Ralidaer/PhotovoltaicSystem/Photos/IMG_20210707_111322.jpg

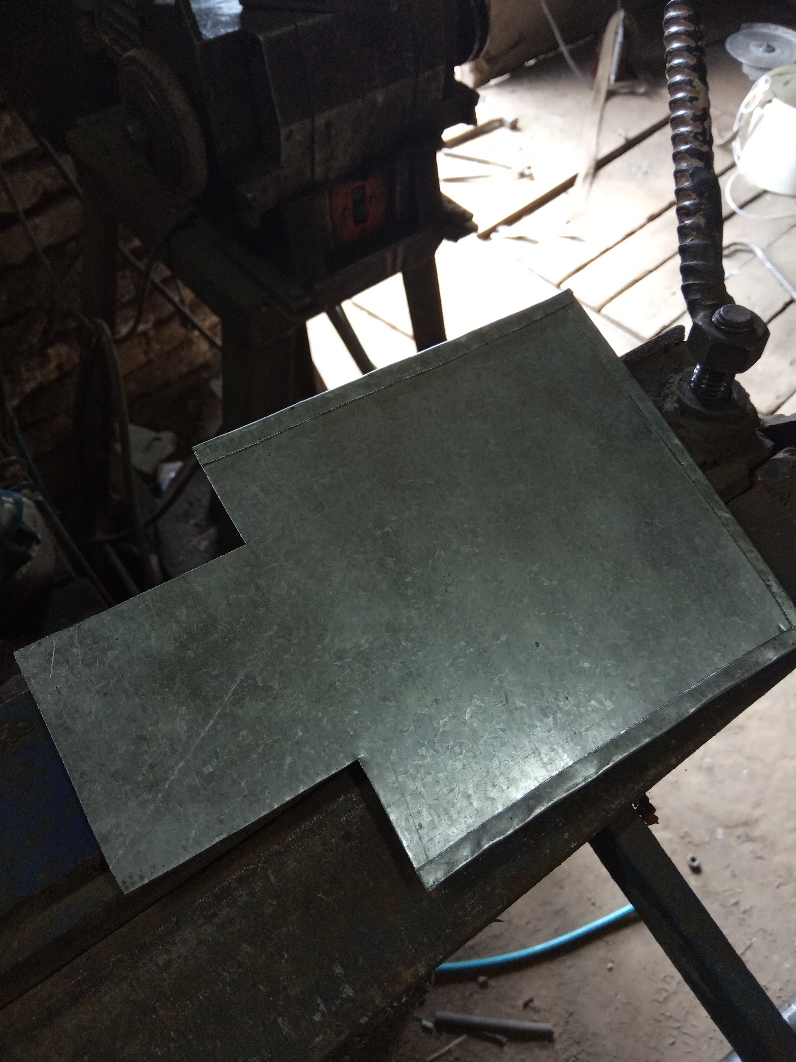
Photos/IMG_20210707_111322.jpg
