Ralidaer/PhotovoltaicSystem/Photos/IMG_20210707_111331.jpg

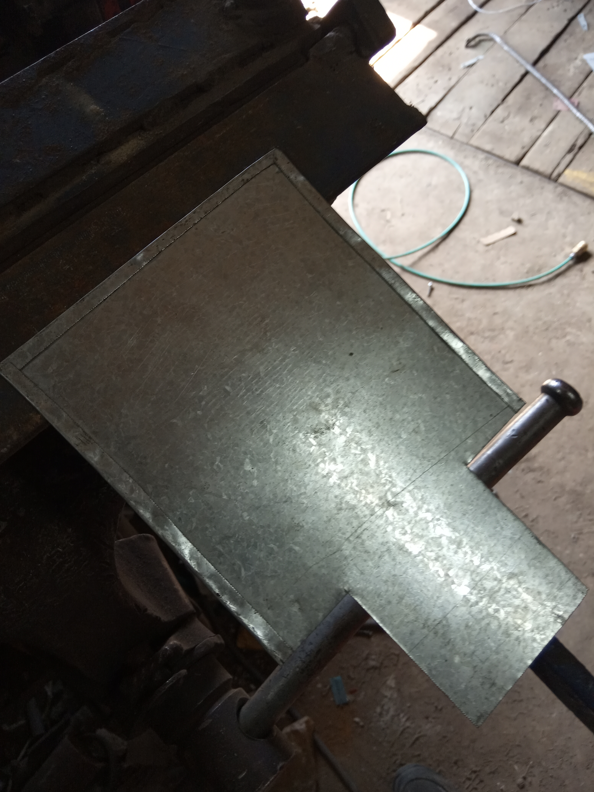
Photos/IMG_20210707_111331.jpg
