Ralidaer/PhotovoltaicSystem/Photos/IMG_20210707_111337.jpg

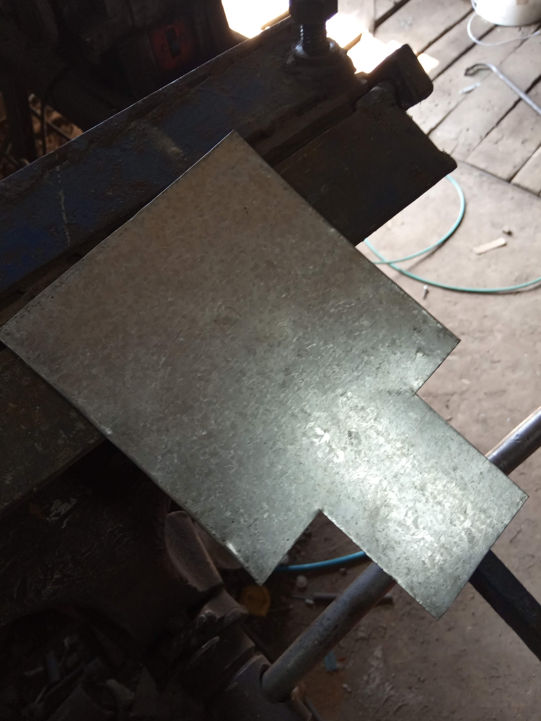
Photos/IMG_20210707_111337.jpg
