Ralidaer/PhotovoltaicSystem/Photos/IMG_20210707_163816.jpg

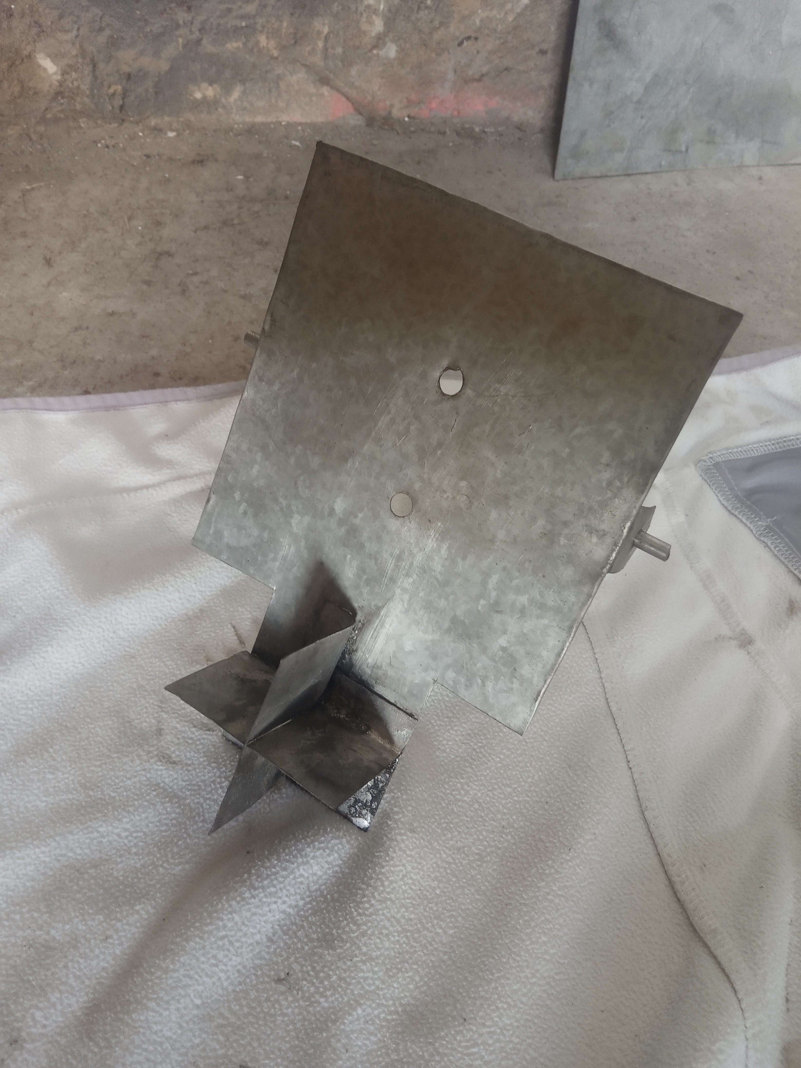
Photos/IMG_20210707_163816.jpg
