Ralidaer/PhotovoltaicSystem/Photos/IMG_20210707_163824.jpg

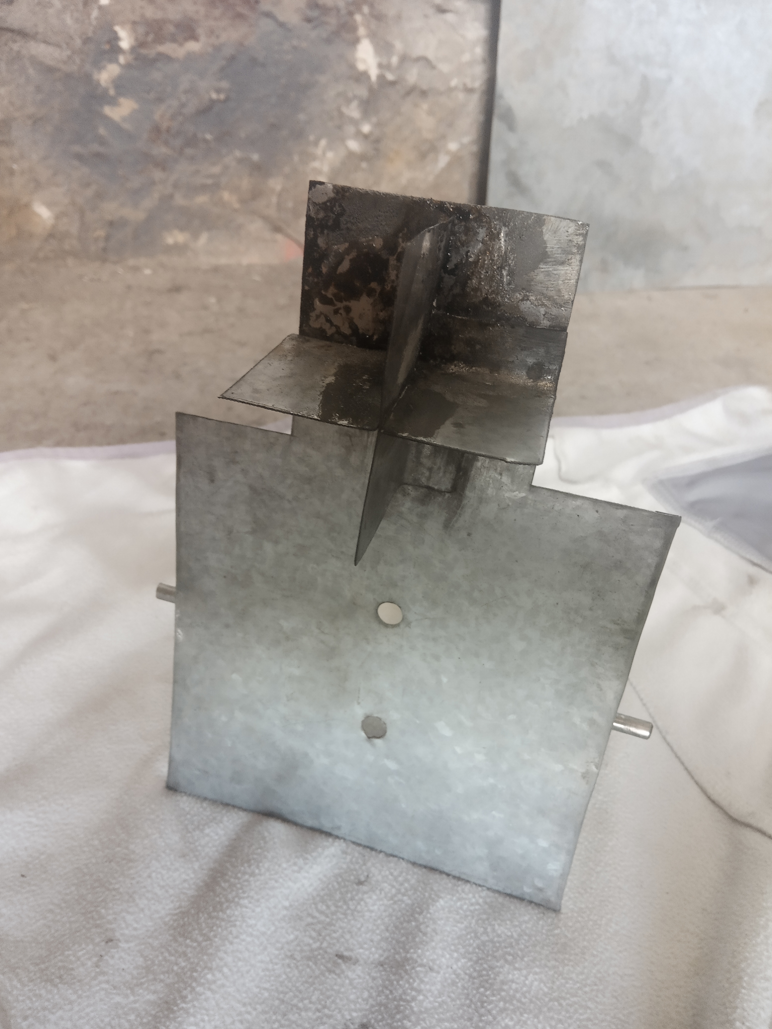
Photos/IMG_20210707_163824.jpg
