Ralidaer/PhotovoltaicSystem/Photos/IMG_20210707_163836.jpg

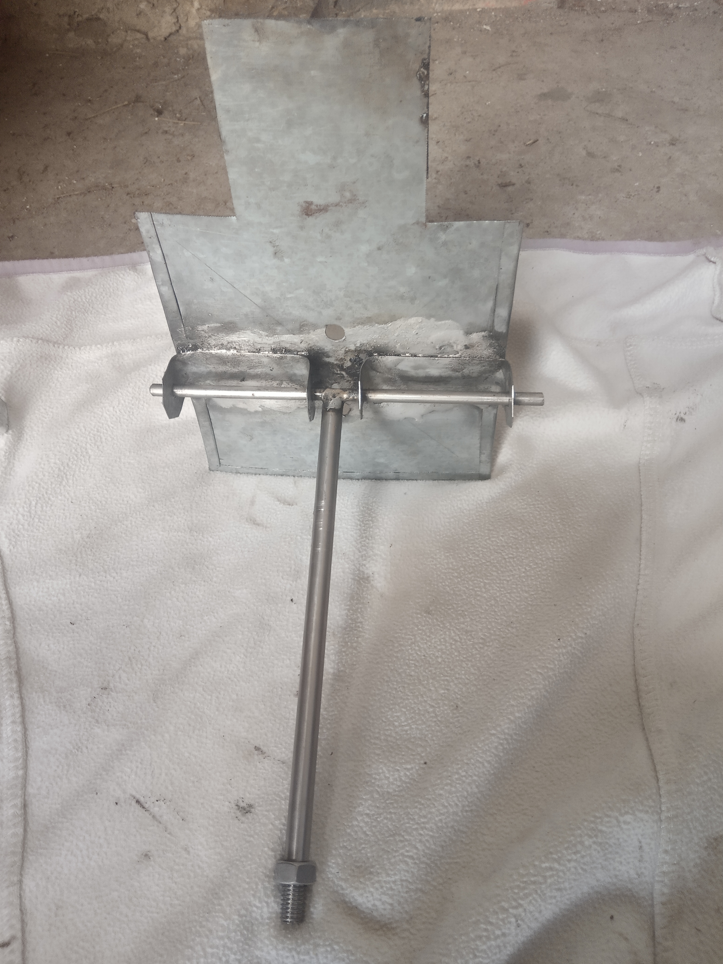
Photos/IMG_20210707_163836.jpg
