Ralidaer/PhotovoltaicSystem/Photos/IMG_20210708_154845.jpg

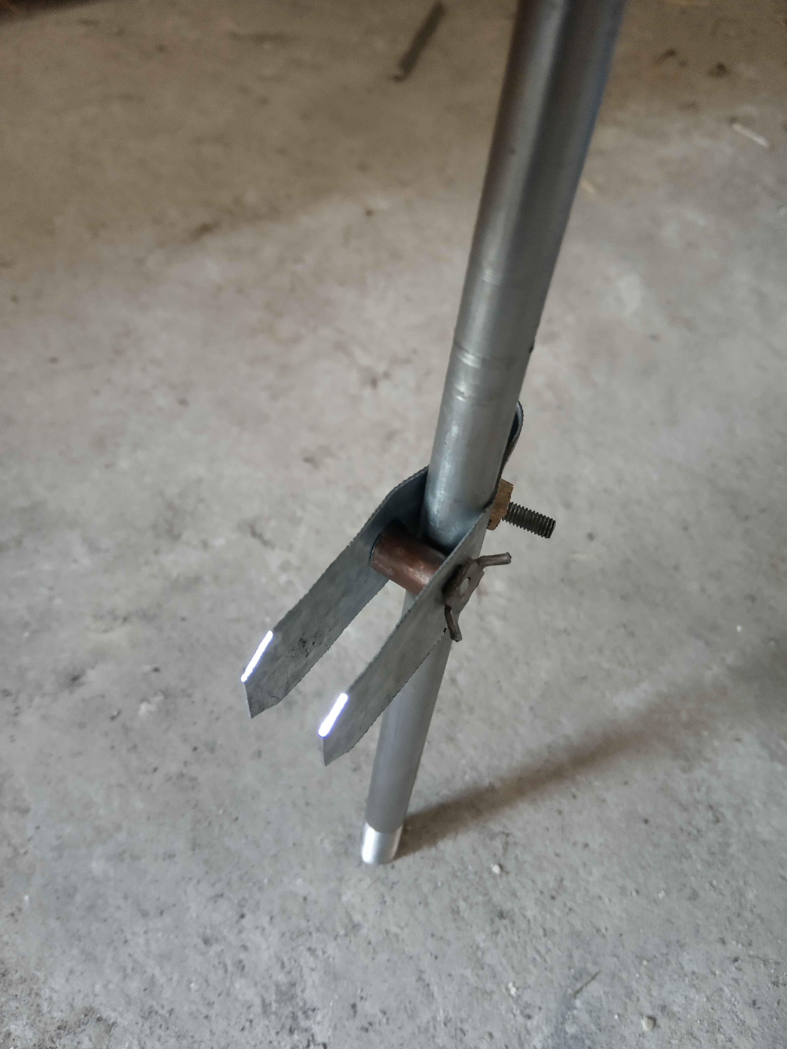
Photos/IMG_20210708_154845.jpg
