Ralidaer/PhotovoltaicSystem/Photos/IMG_20210708_154850.jpg

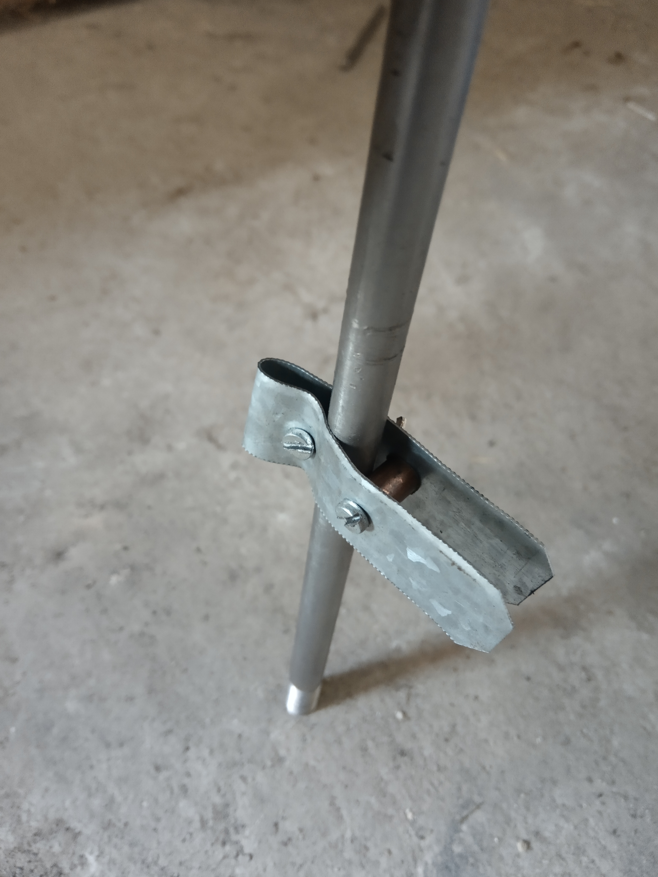
Photos/IMG_20210708_154850.jpg
