Ralidaer/PhotovoltaicSystem/Photos/IMG_20210709_112318.jpg

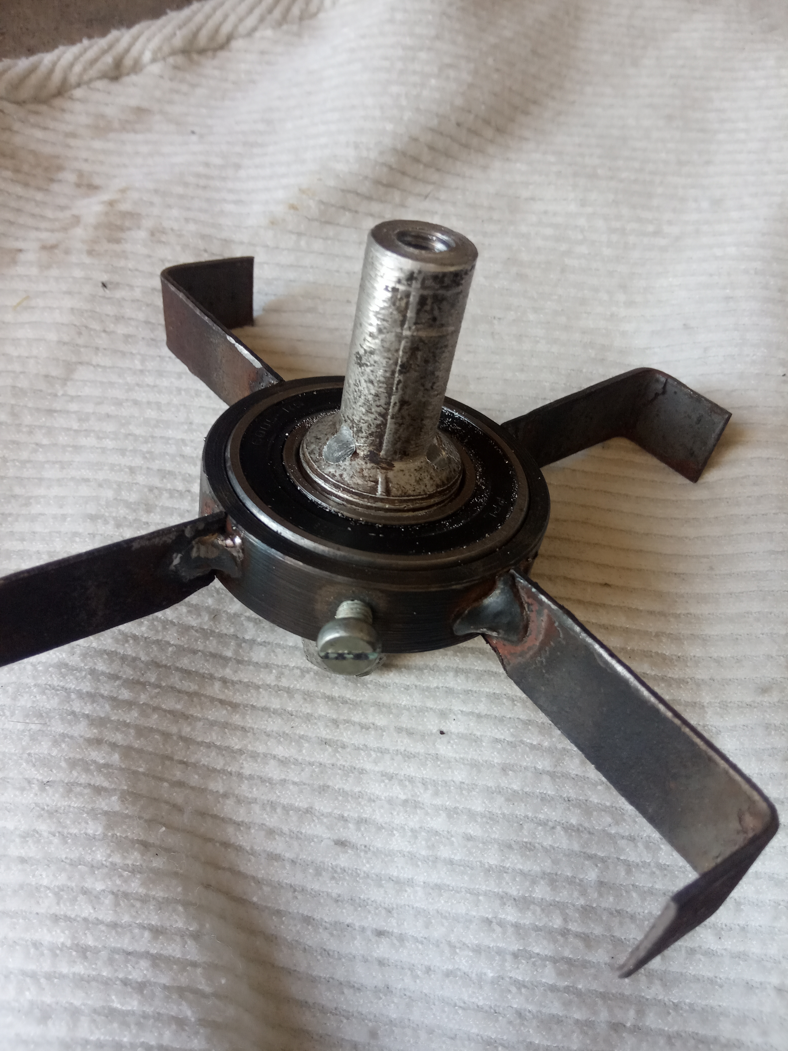
Photos/IMG_20210709_112318.jpg
