Ralidaer/PhotovoltaicSystem/Photos/IMG_20210709_112324.jpg

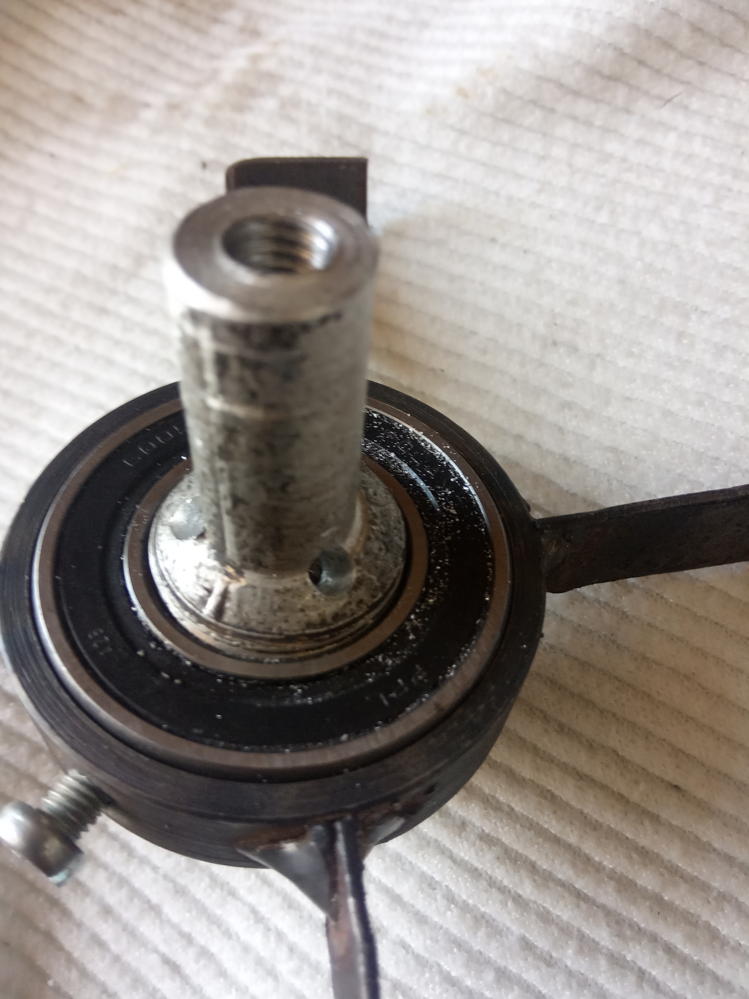
Photos/IMG_20210709_112324.jpg
