Ralidaer/PhotovoltaicSystem/Photos/IMG_20210709_112329.jpg

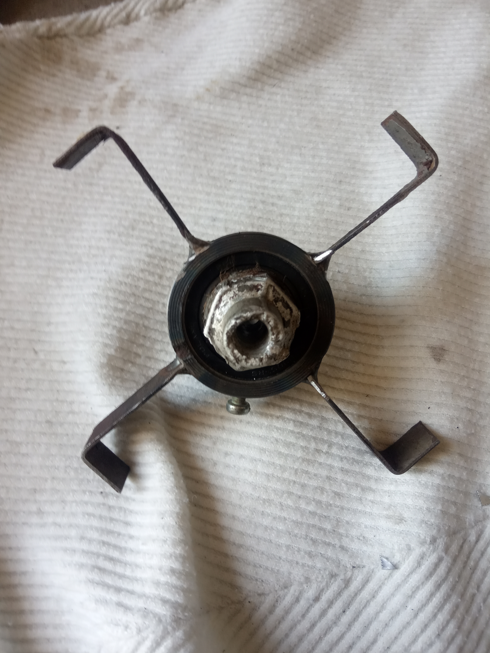
Photos/IMG_20210709_112329.jpg
