Ralidaer/PhotovoltaicSystem/Photos/IMG_20210709_112338.jpg

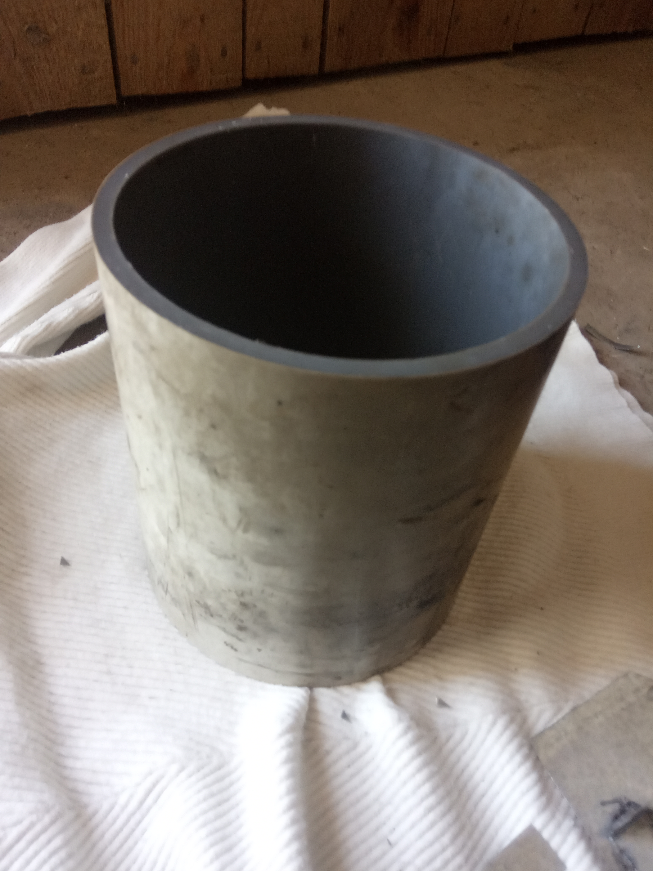
Photos/IMG_20210709_112338.jpg
