Ralidaer/PhotovoltaicSystem/Photos/IMG_20210709_112344.jpg

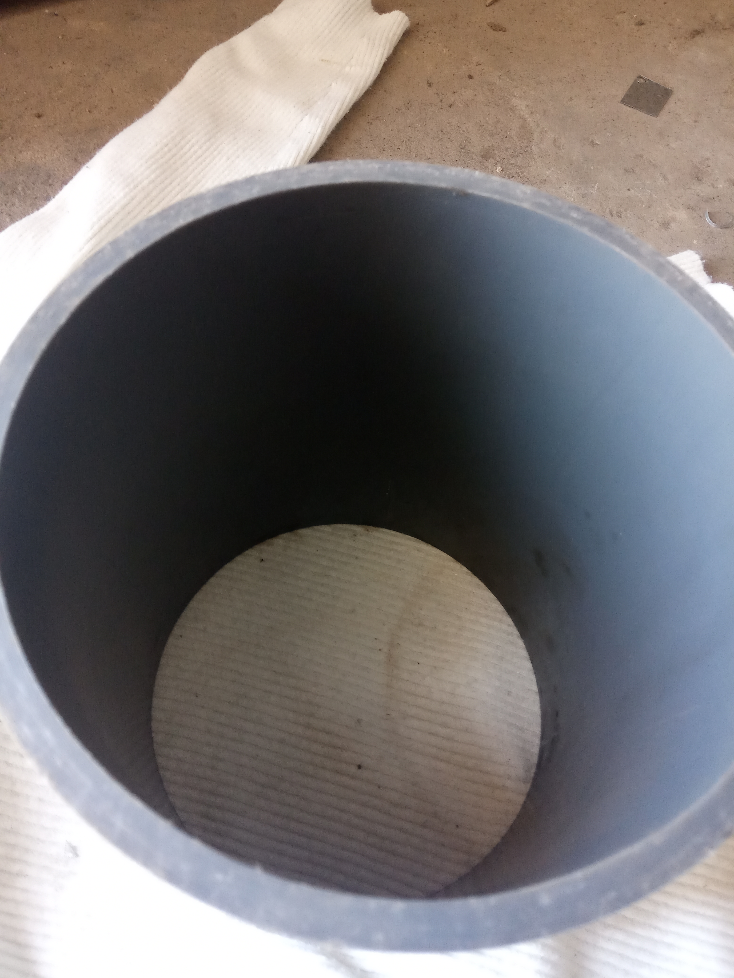
Photos/IMG_20210709_112344.jpg
