Ralidaer/PhotovoltaicSystem/Photos/IMG_20210709_112456.jpg

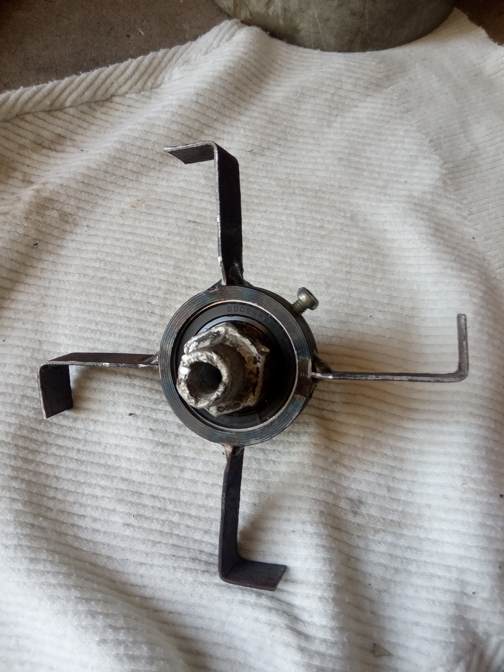
Photos/IMG_20210709_112456.jpg
