Ralidaer/PhotovoltaicSystem/Photos/IMG_20210709_112603.jpg

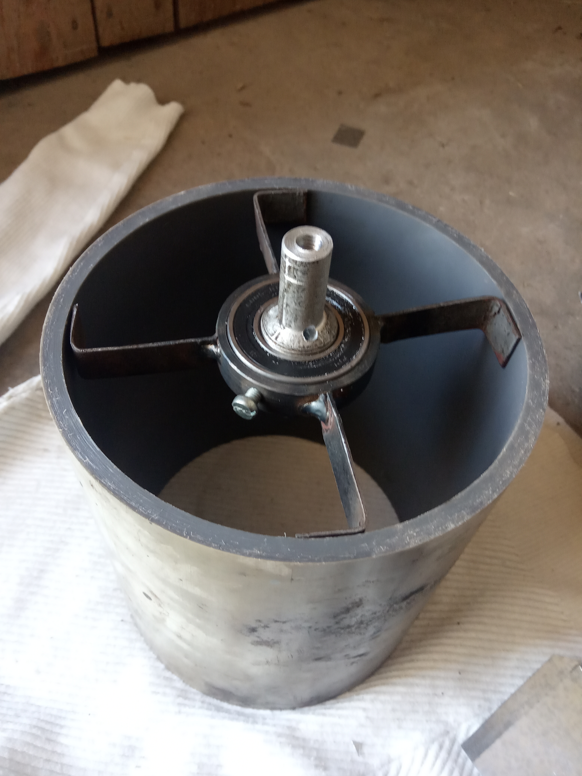
Photos/IMG_20210709_112603.jpg
