Ralidaer/PhotovoltaicSystem/Photos/IMG_20210709_112611.jpg

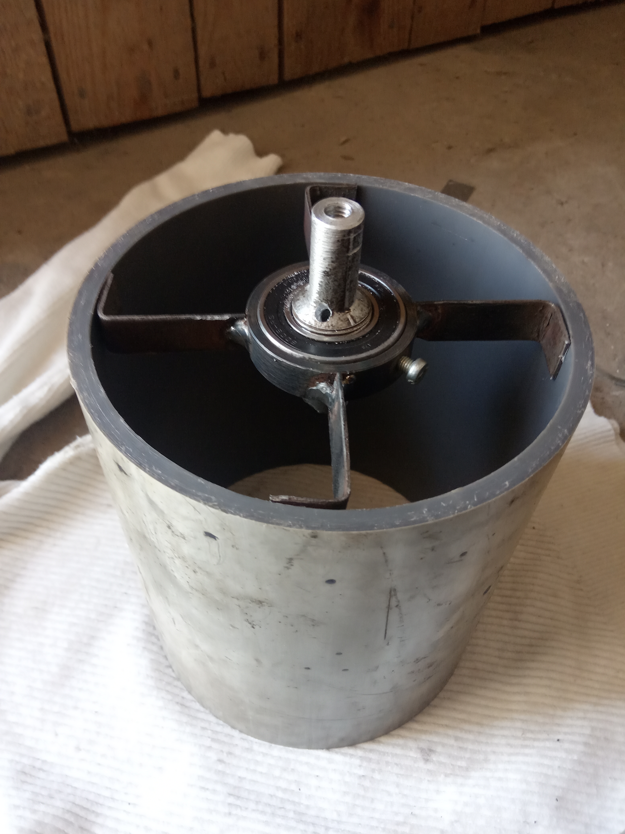
Photos/IMG_20210709_112611.jpg
