Ralidaer/PhotovoltaicSystem/Photos/IMG_20210709_112644.jpg

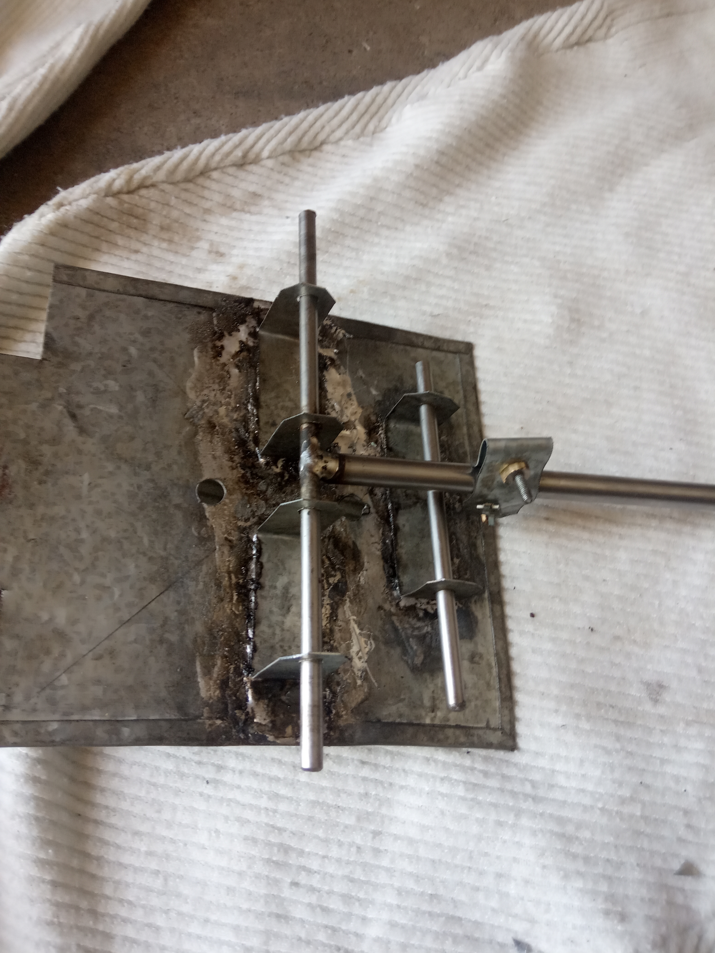
Photos/IMG_20210709_112644.jpg
