Ralidaer/PhotovoltaicSystem/Photos/IMG_20210709_112650.jpg

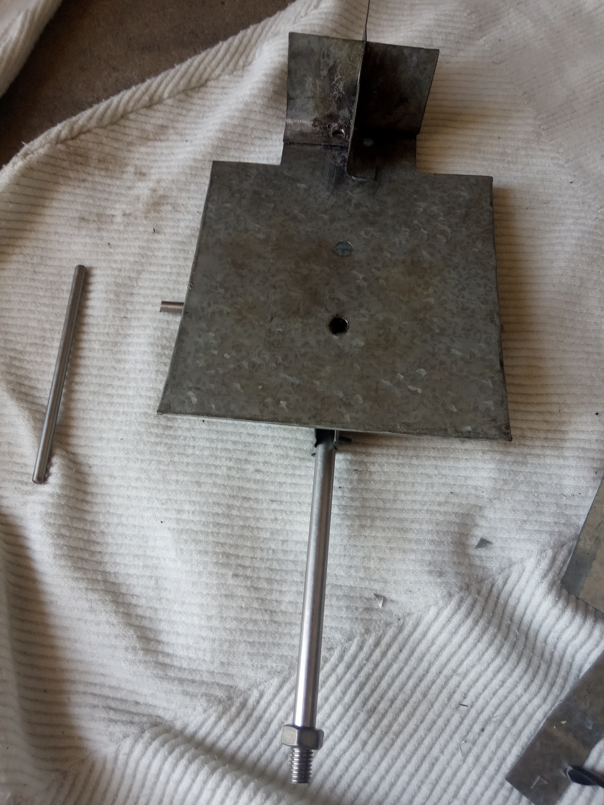
Photos/IMG_20210709_112650.jpg
