Ralidaer/PhotovoltaicSystem/Photos/IMG_20210709_112700.jpg

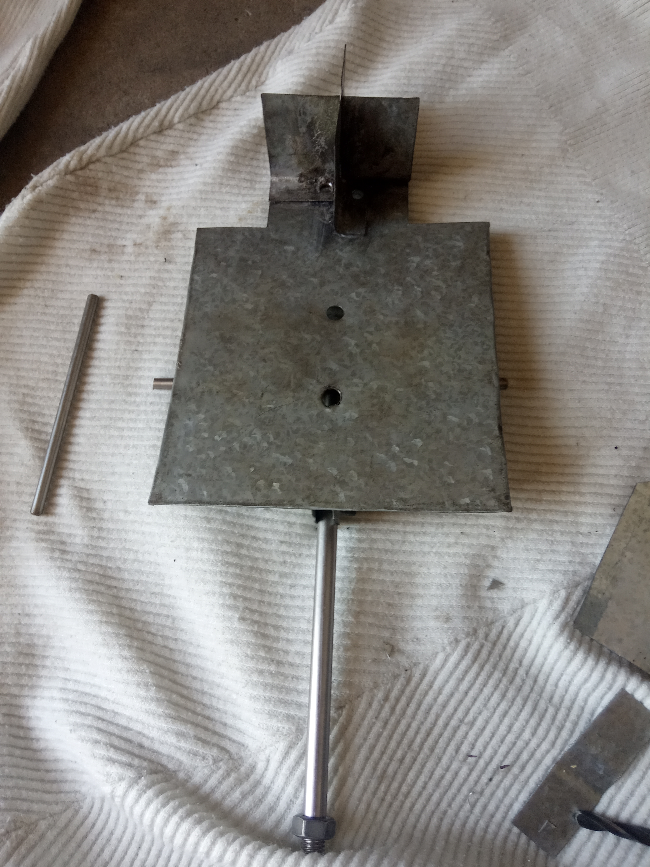
Photos/IMG_20210709_112700.jpg
