Ralidaer/PhotovoltaicSystem/Photos/IMG_20210709_112758.jpg

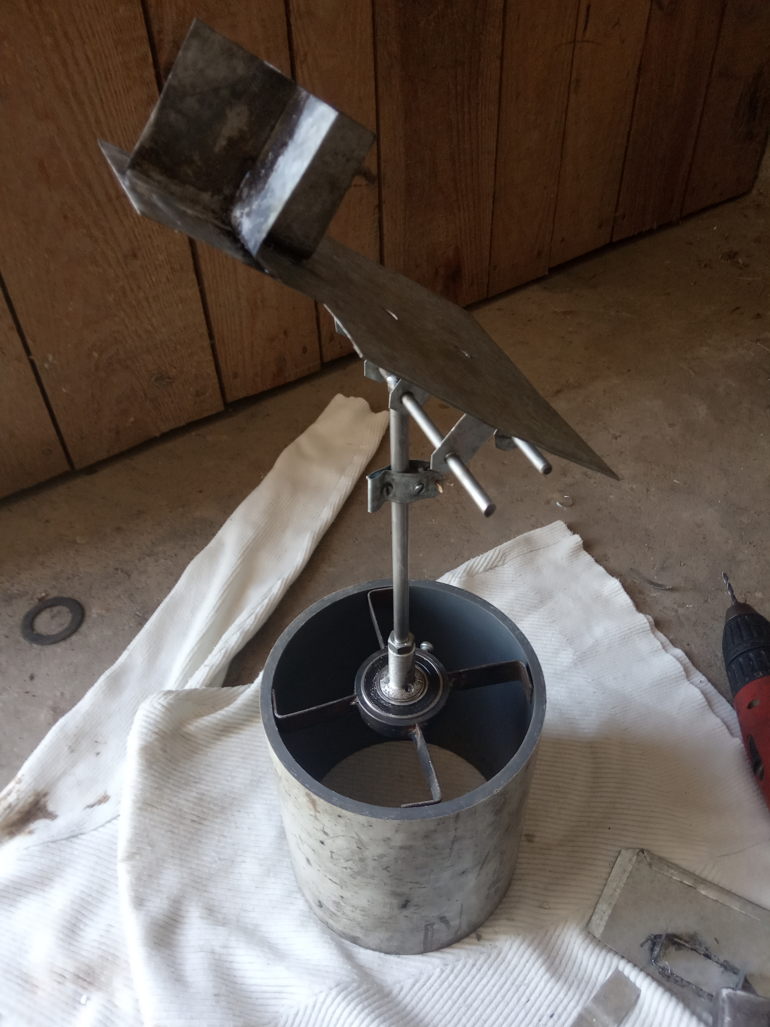
Photos/IMG_20210709_112758.jpg
