Ralidaer/PhotovoltaicSystem/Photos/IMG_20210709_112804.jpg

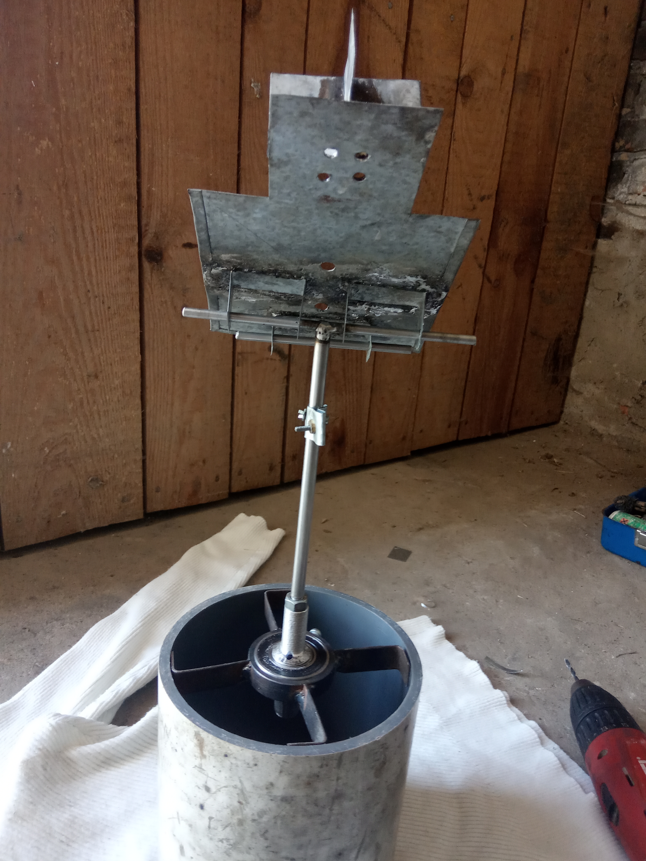
Photos/IMG_20210709_112804.jpg
