Ralidaer/PhotovoltaicSystem/Photos/IMG_20210709_112812.jpg

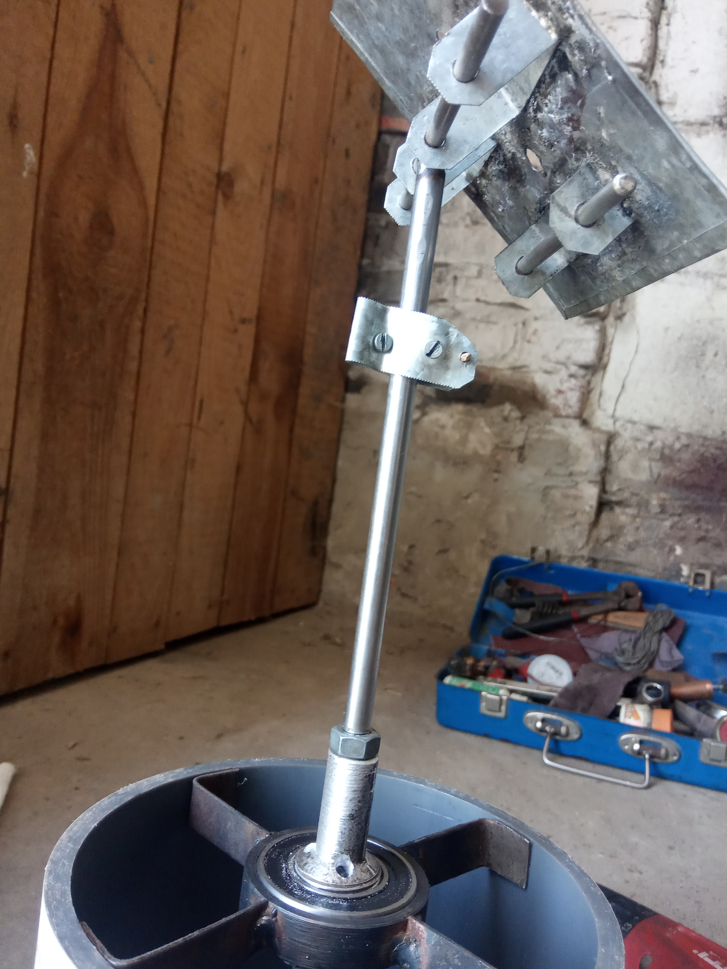
Photos/IMG_20210709_112812.jpg
