Ralidaer/PhotovoltaicSystem/Photos/IMG_20210728_113514.jpg

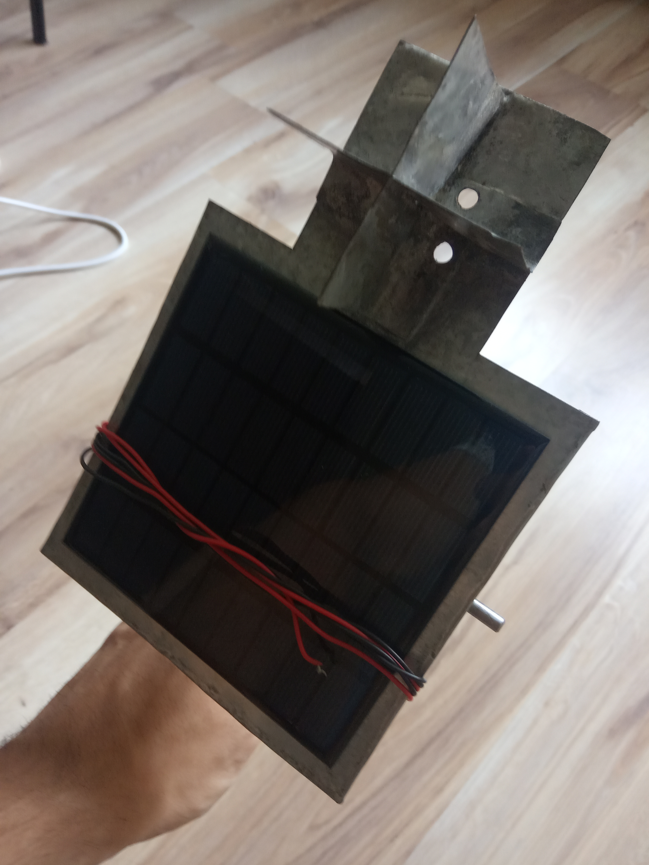
Photos/IMG_20210728_113514.jpg
