Ralidaer/PhotovoltaicSystem/Photos/IMG_20210728_113616.jpg

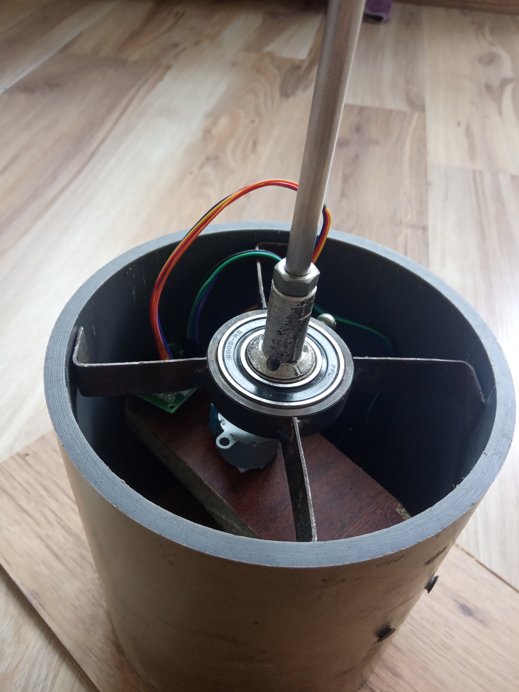
Photos/IMG_20210728_113616.jpg
