Ralidaer/PhotovoltaicSystem/Photos/IMG_20210728_113623.jpg

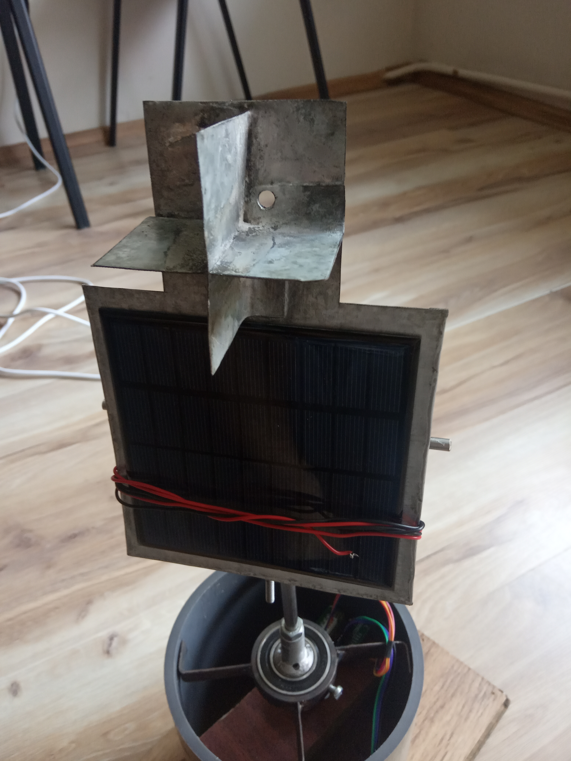
Photos/IMG_20210728_113623.jpg
