Ralidaer/PhotovoltaicSystem/Photos/IMG_20210728_113631.jpg

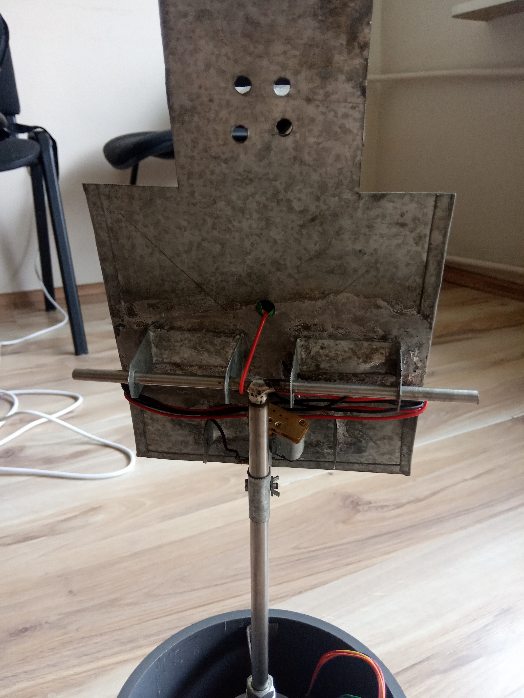
Photos/IMG_20210728_113631.jpg
