Ralidaer/PhotovoltaicSystem/Photos/IMG_20210728_113649.jpg

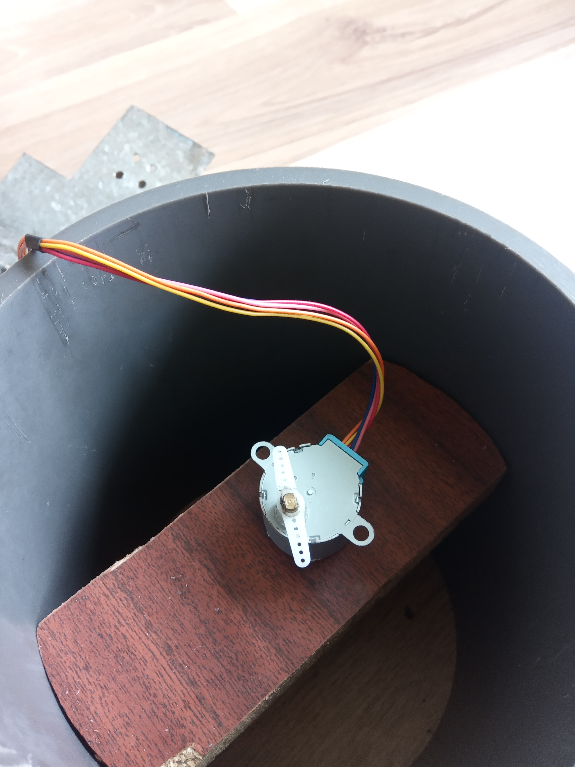
Photos/IMG_20210728_113649.jpg
