Ralidaer/PhotovoltaicSystem/Photos/IMG_20210728_113656.jpg

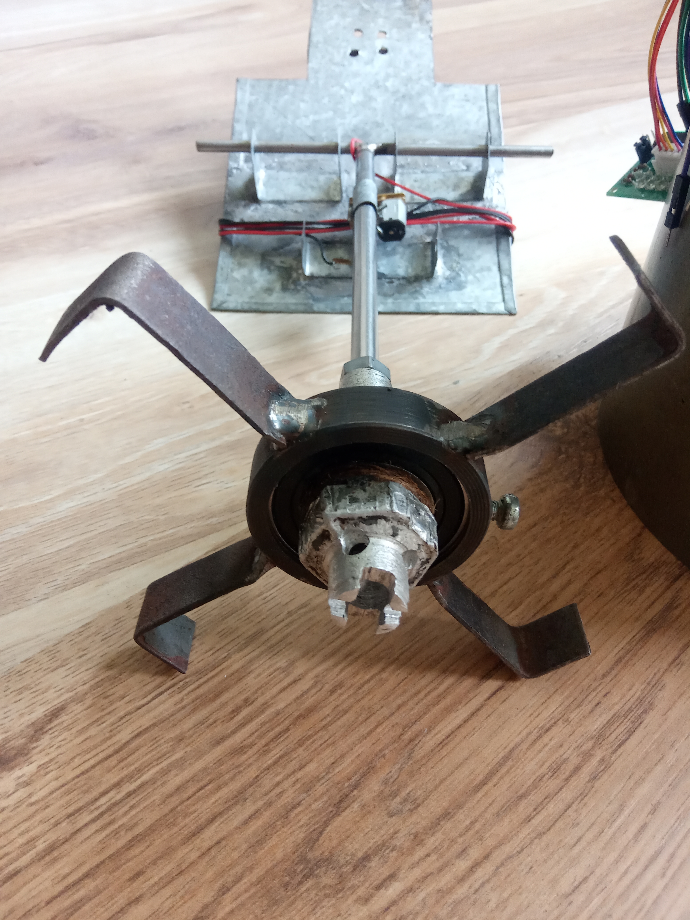
Photos/IMG_20210728_113656.jpg
