Ralidaer/PhotovoltaicSystem/Photos/IMG_20210728_113701.jpg

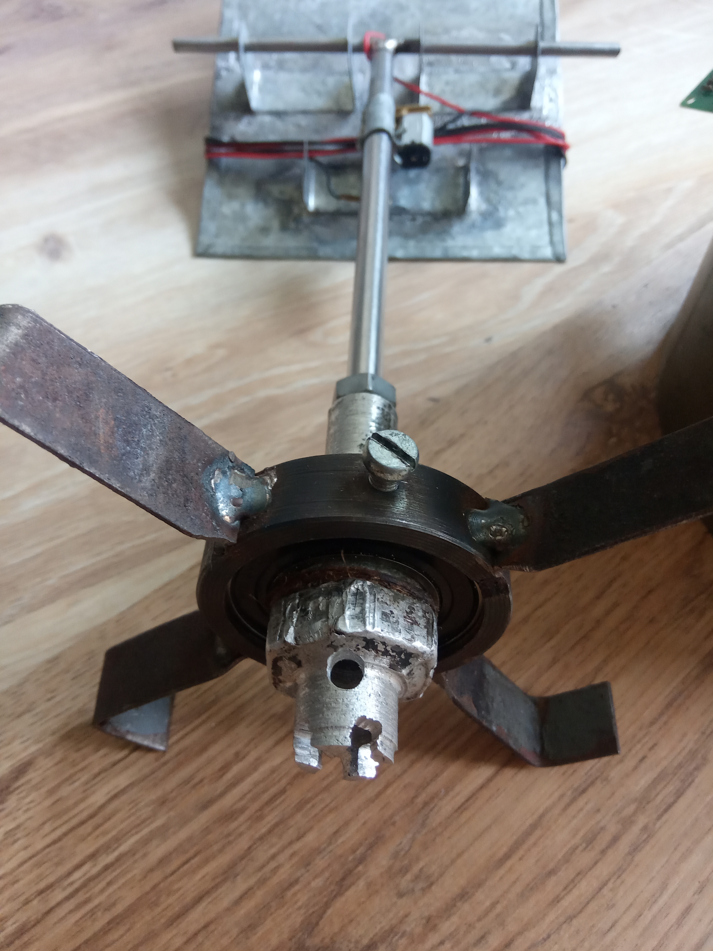
Photos/IMG_20210728_113701.jpg
