Ralidaer/PhotovoltaicSystem/Photos/IMG_20210728_113719.jpg

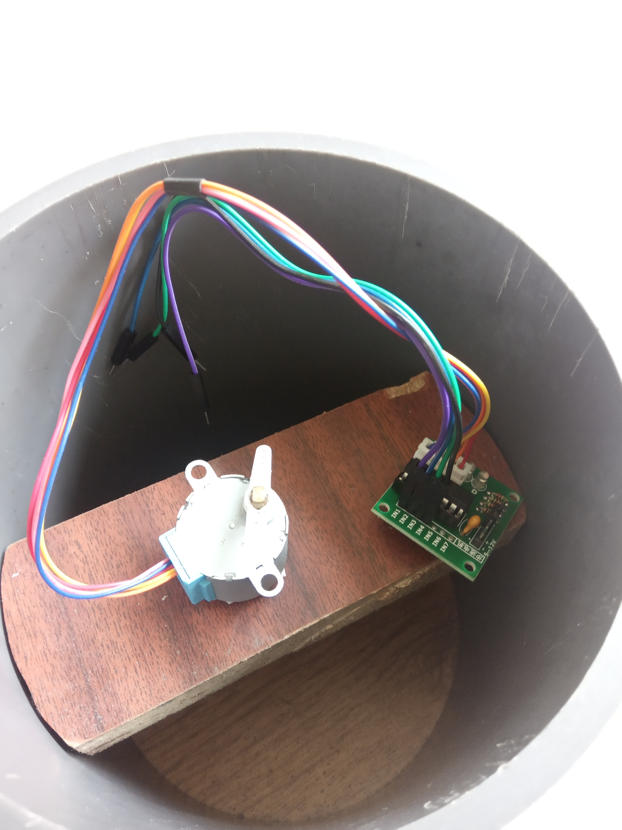
Photos/IMG_20210728_113719.jpg
