Ralidaer/PhotovoltaicSystem/Photos/IMG_20210728_131431.jpg

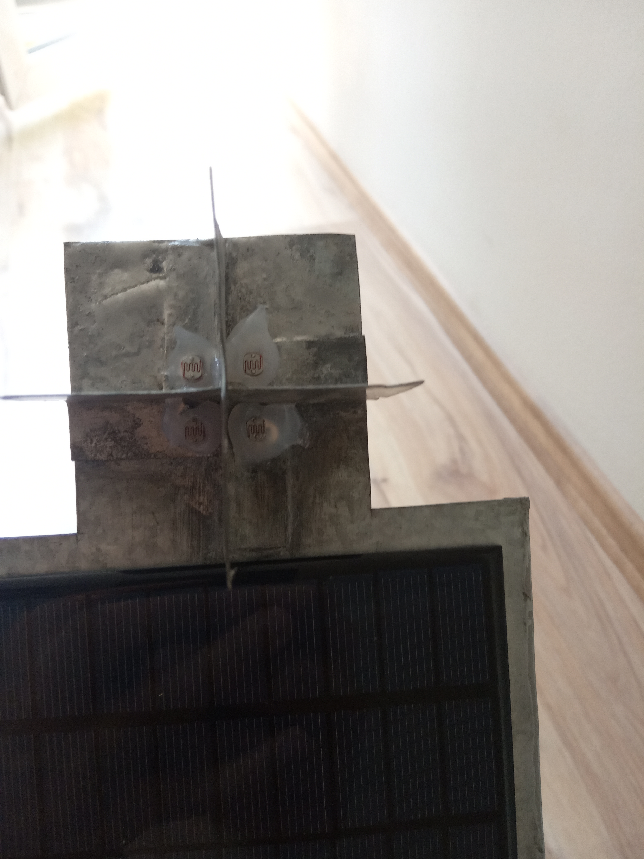
Photos/IMG_20210728_131431.jpg
