Ralidaer/PhotovoltaicSystem/Photos/IMG_20210728_131442.jpg

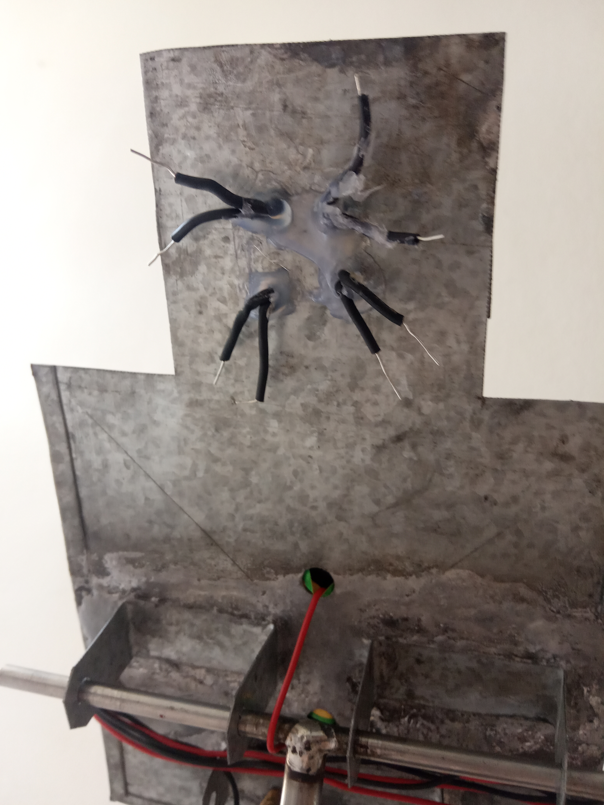
Photos/IMG_20210728_131442.jpg
