Ralidaer/PhotovoltaicSystem/Photos/IMG_20210728_131450.jpg

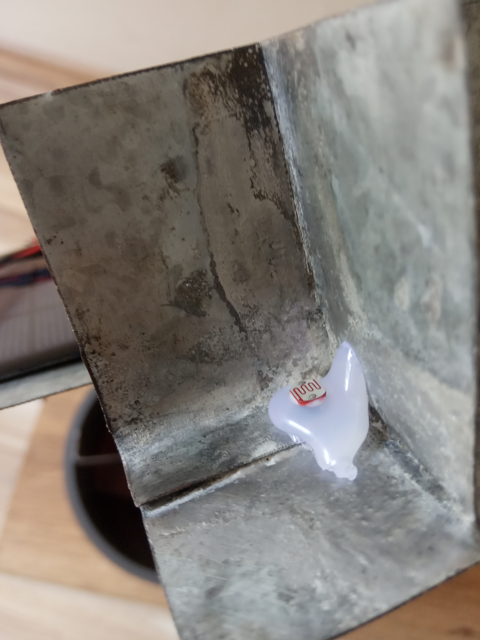
Photos/IMG_20210728_131450.jpg
