Ralidaer/PhotovoltaicSystem/Photos/IMG_20210911_135315.jpg

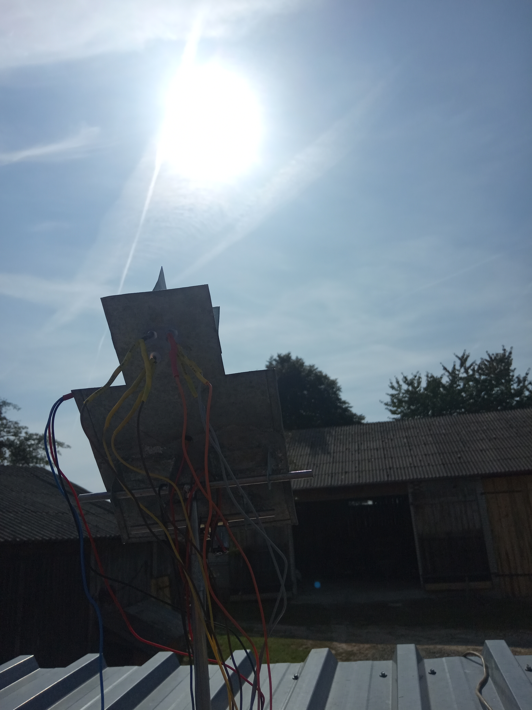
Photos/IMG_20210911_135315.jpg
