Ralidaer/PhotovoltaicSystem/Photos/IMG_20210911_135330.jpg

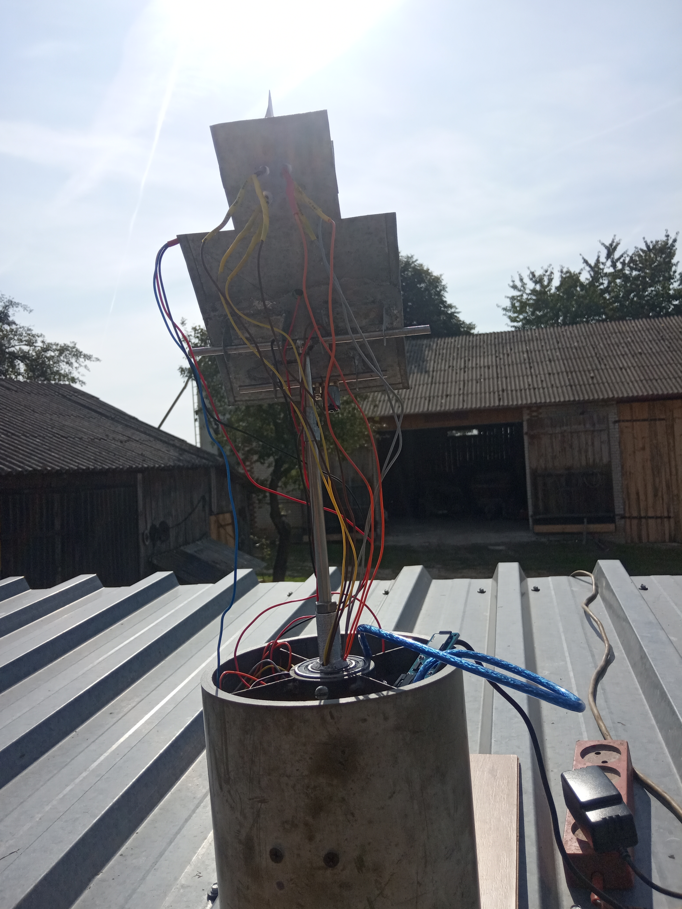
Photos/IMG_20210911_135330.jpg
