Ralidaer/PhotovoltaicSystem/Photos/IMG_20210911_135332.jpg

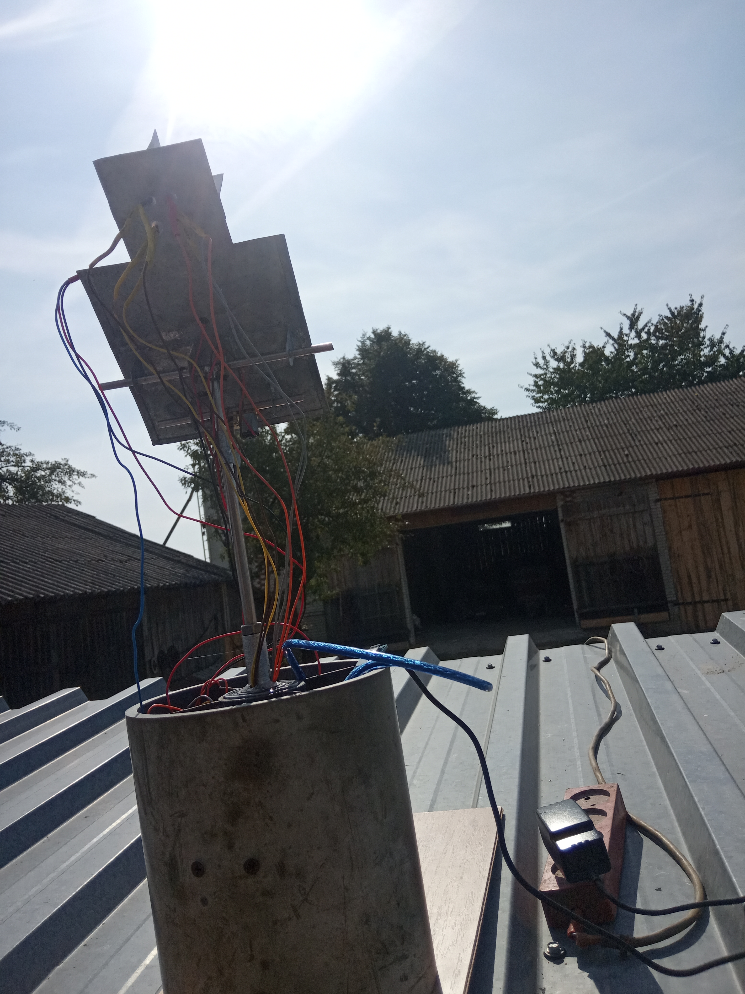
Photos/IMG_20210911_135332.jpg
