Ralidaer/PhotovoltaicSystem/Photos/IMG_20210911_135337.jpg

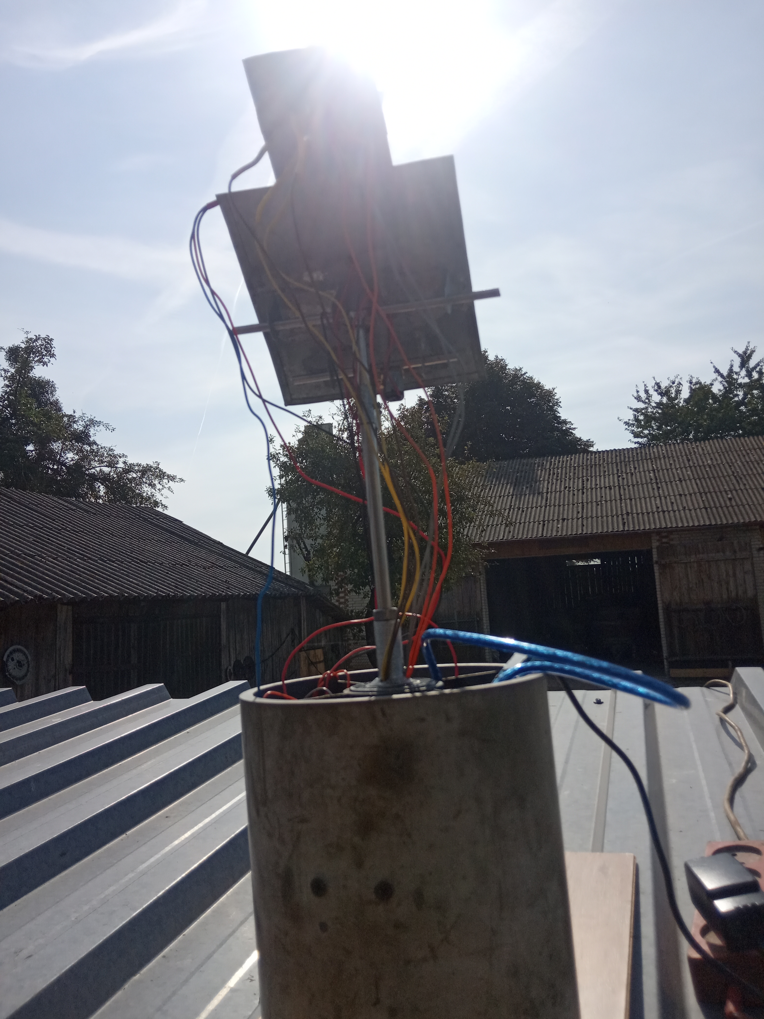
Photos/IMG_20210911_135337.jpg
