Ralidaer/PhotovoltaicSystem/Photos/IMG_20210912_131358.jpg

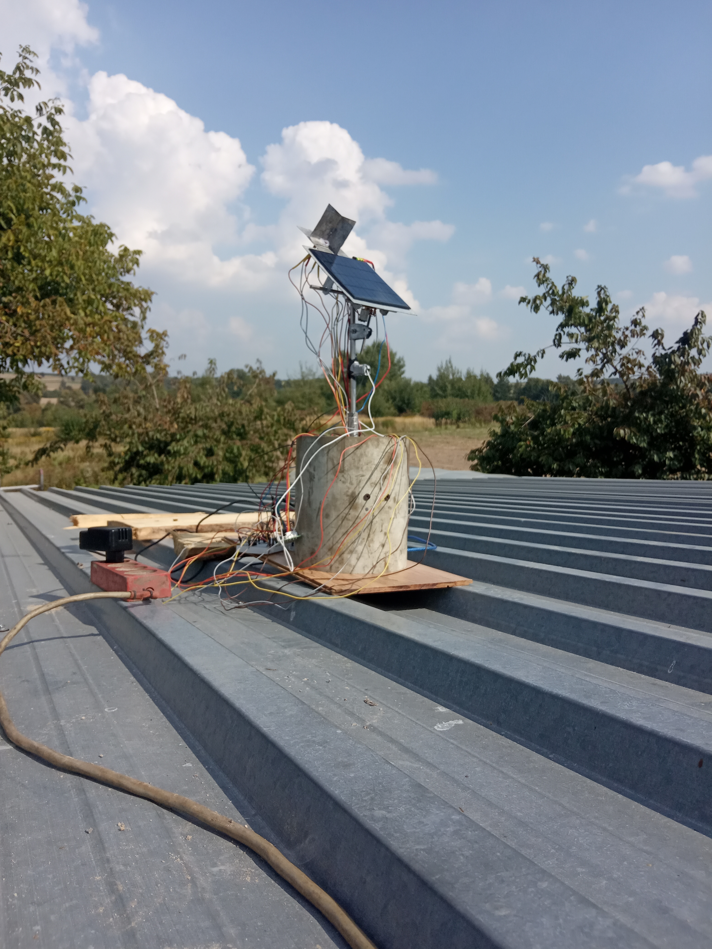
Photos/IMG_20210912_131358.jpg
