Ralidaer/PhotovoltaicSystem/pomiary/analiza/5.38.png

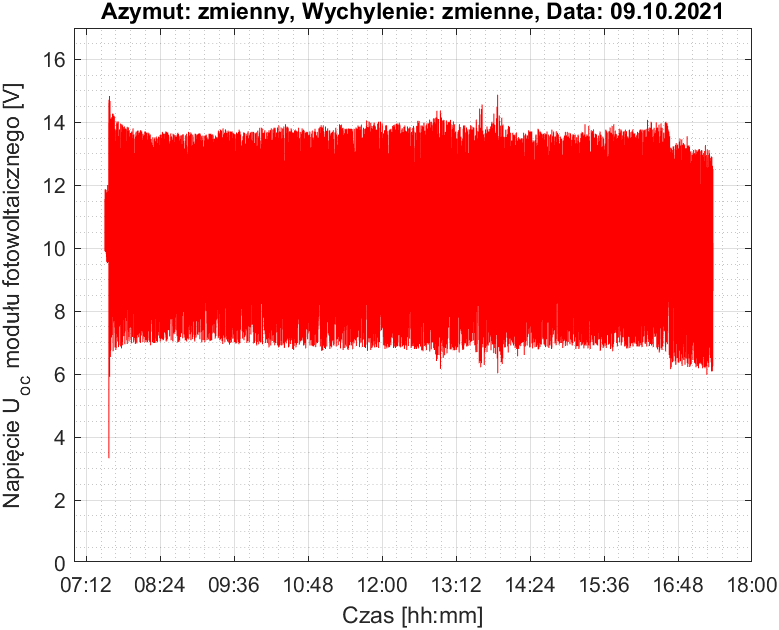
pomiary/analiza/5.38.png
