Ralidaer/PhotovoltaicSystem/pomiary/analiza/5.39.png

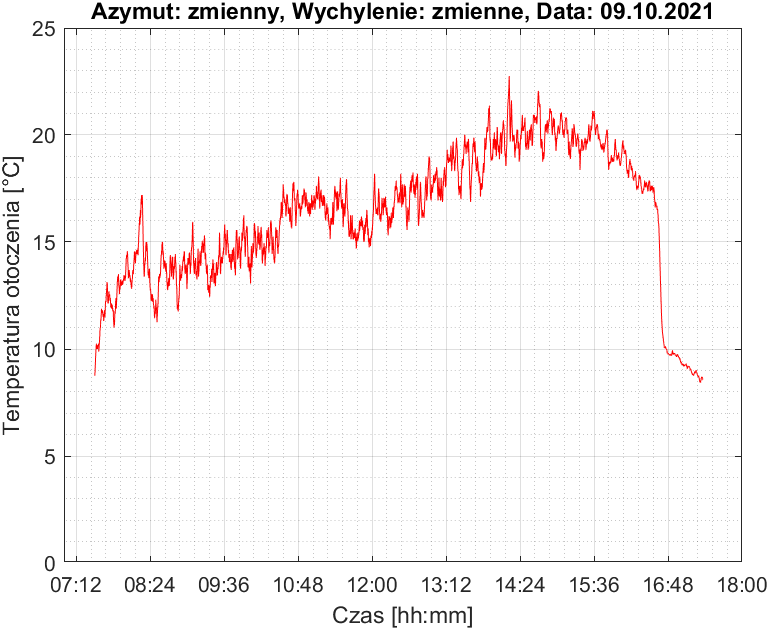
pomiary/analiza/5.39.png
