Ralidaer/PhotovoltaicSystem/pomiary/analiza/5.40.png

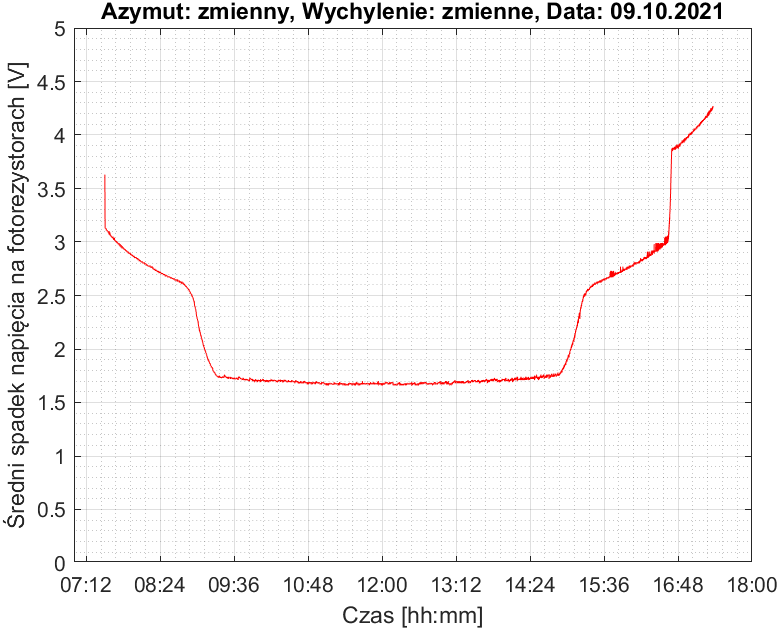
pomiary/analiza/5.40.png
