Ralidaer/PhotovoltaicSystem/pomiary/analiza/5.41.png

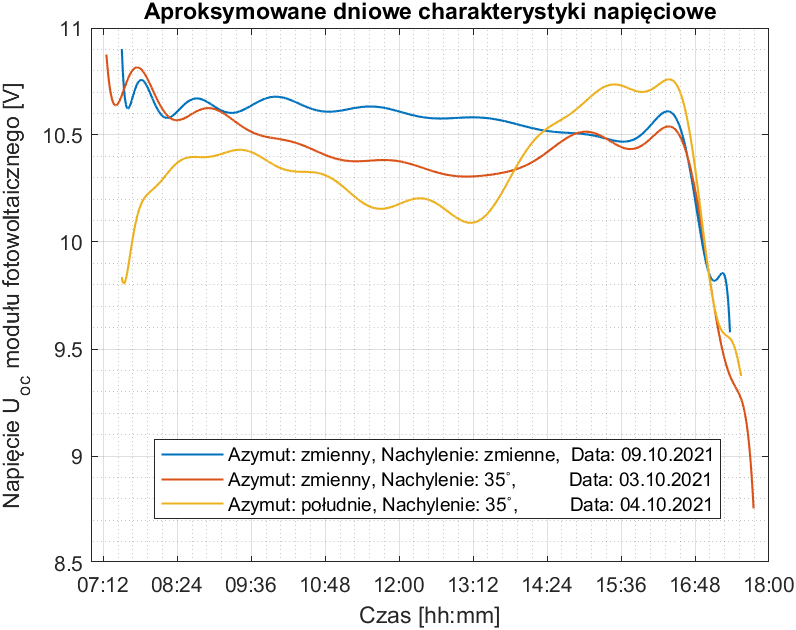
pomiary/analiza/5.41.png
