Ralidaer/PhotovoltaicSystem/pomiary/analiza/5.42.png

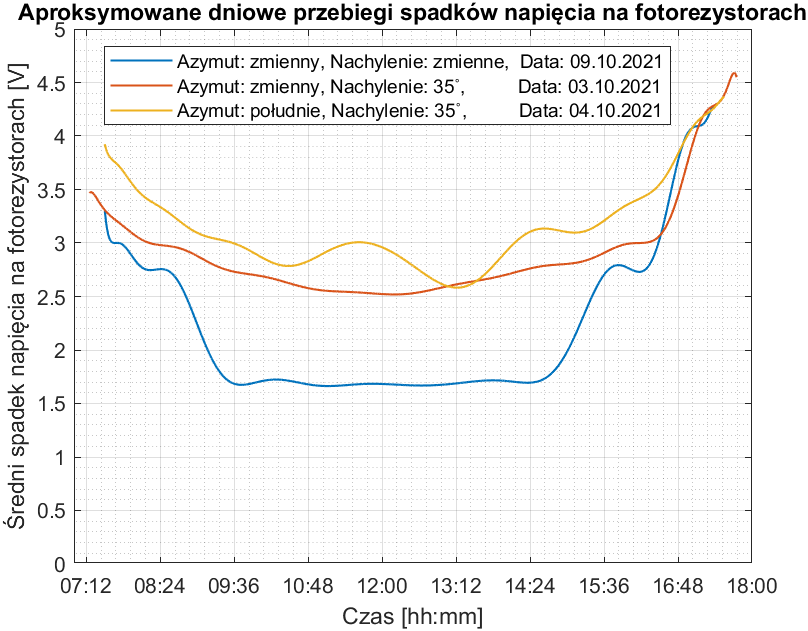
pomiary/analiza/5.42.png
